vanpit/Tang-20K-41464-DRAM-tester/Pictures/20260316_213155.jpg

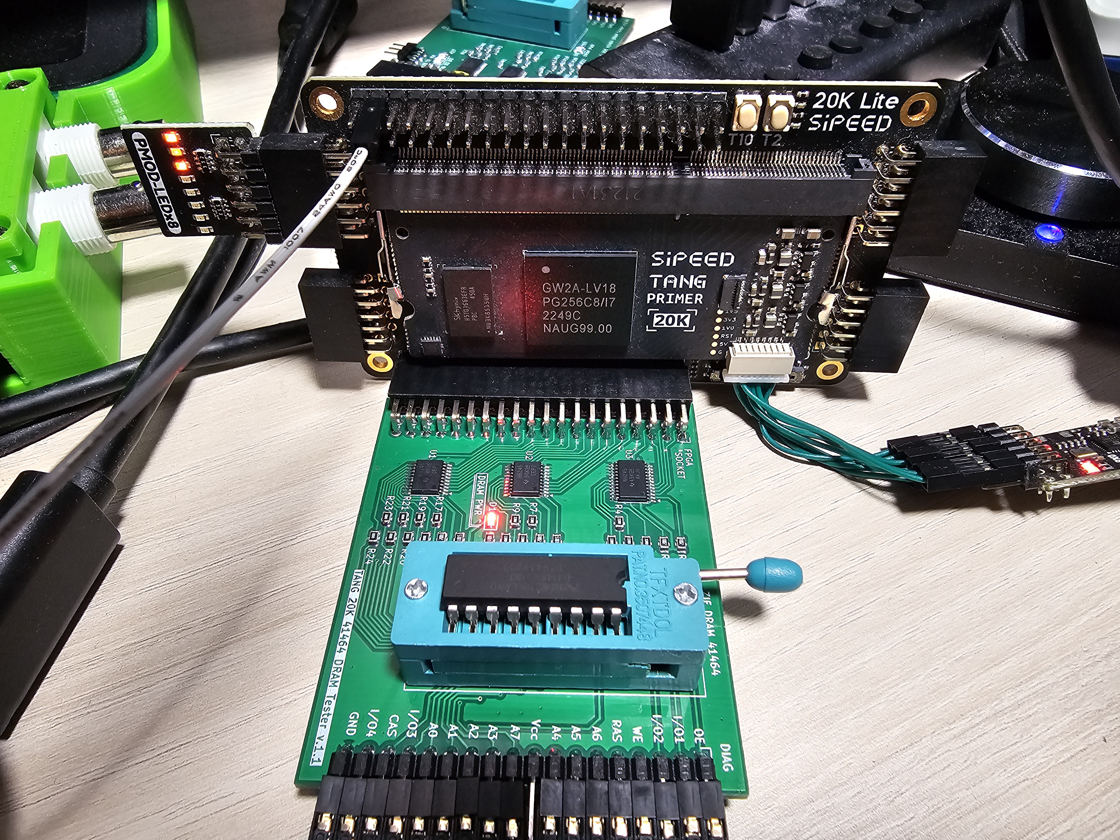
Pictures/20260316_213155.jpg
