vanpit/Tang-20K-41464-DRAM-tester/Firmware/Tang 41464 dram tester Nano/src/gowin_rpll/gowin_rpll_tmp.v

//Copyright (C)2014-2025 Gowin Semiconductor Corporation.
//All rights reserved.
//File Title: Template file for instantiation
//Tool Version: V1.9.11.03 Education
//Part Number: GW2AR-LV18QN88C8/I7
//Device: GW2AR-18
//Device Version: C
//Created Time: Tue Mar 24 17:58:03 2026

//Change the instance name and port connections to the signal names
//--------Copy here to design--------

    Gowin_rPLL your_instance_name(
        .clkout(clkout), //output clkout
        .lock(lock), //output lock
        .clkin(clkin) //input clkin
    );

//--------Copy end-------------------
