vanpit/Tang-20K-41464-DRAM-tester/Firmware/Tang 41464 dram tester Nano/src/uart_tx_opts_pkg.v

package uart_tx_opts_pkg;

    localparam DISP_OPT_MSG_MENU_HEADER   = 0;
    localparam DISP_OPT_MSG_RUNNING       = 1;
    localparam DISP_OPT_MSG_PASS          = 2;
    localparam DISP_OPT_MSG_FAIL          = 3;    
    localparam DISP_OPT_MSG_CONFIG        = 4;
    localparam DISP_OPT_MSG_PROGRESS      = 5;

endpackage
