vanpit/Tang-20K-41464-DRAM-tester/Pictures/20260324_182230.jpg

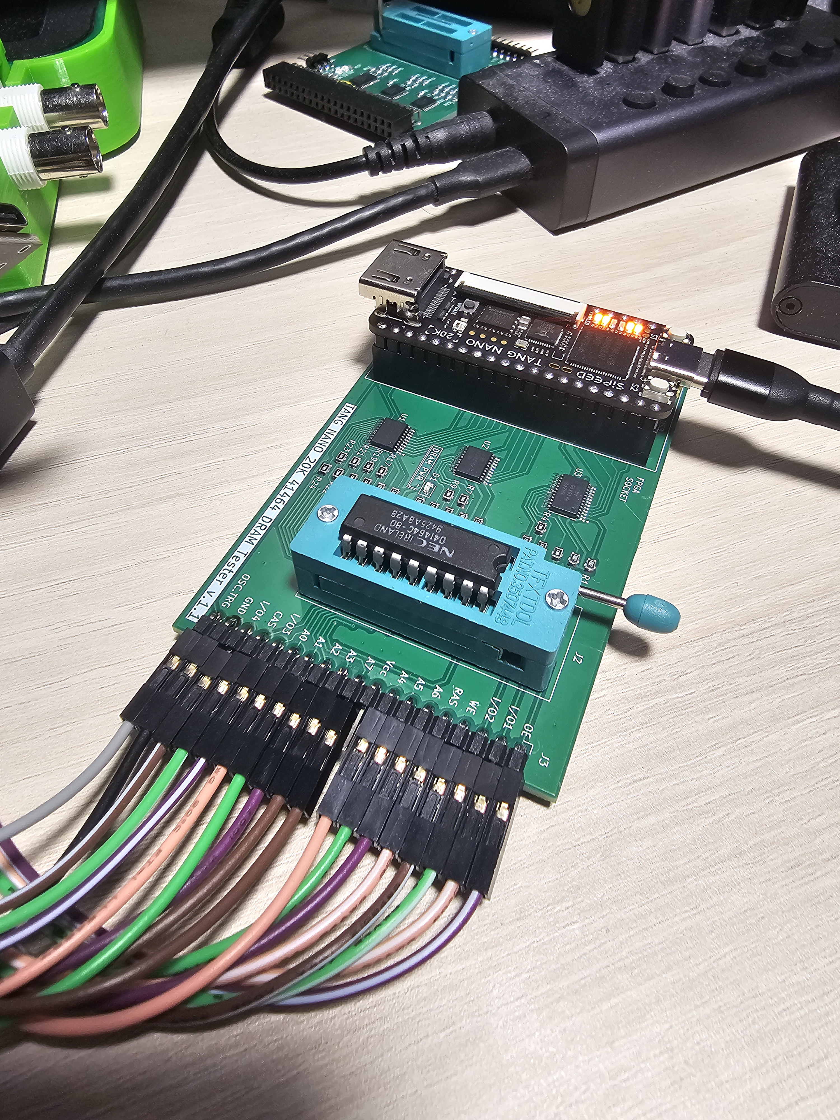
Pictures/20260324_182230.jpg
